aylaa2/tsc-proiect/Images/baterie.png

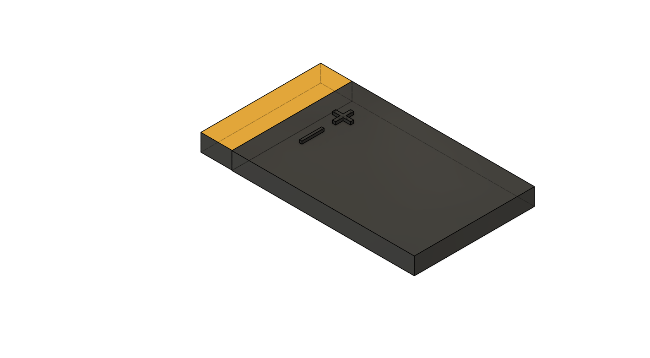
Images/baterie.png
