aylaa2/tsc-proiect/Images/display.png

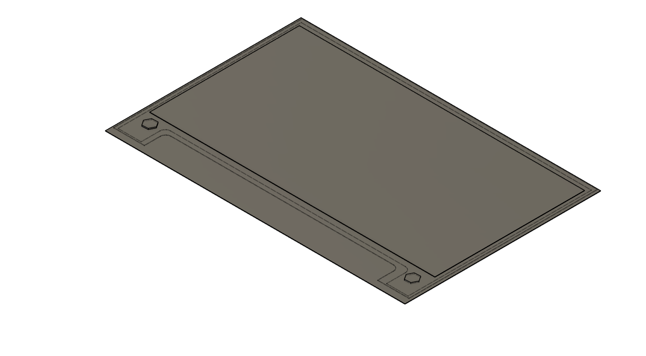
Images/display.png
