aylaa2/tsc-proiect/Images/image.png

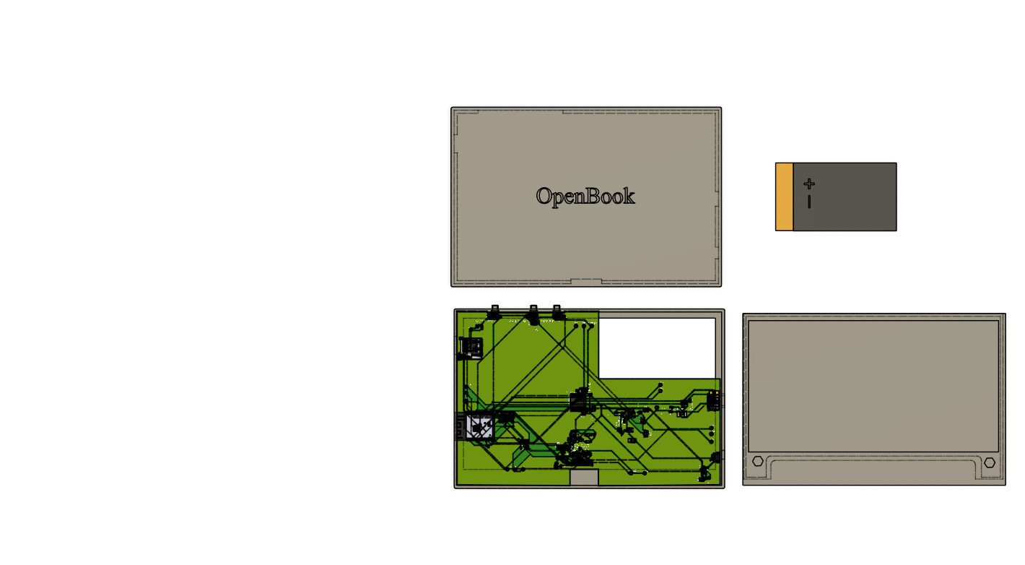
Images/image.png
